UQAM-2023-2026/SYNAPSE/scripts/Python/DT/NSGA-II/data/BottomFloor.png

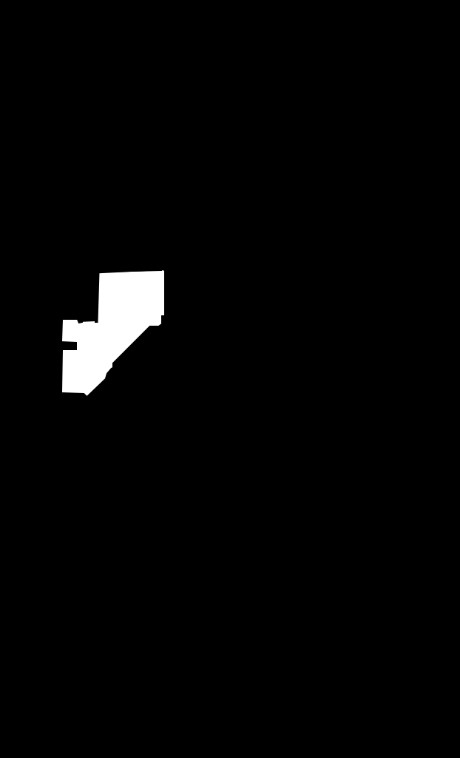
scripts/Python/DT/NSGA-II/data/BottomFloor.png
