UQAM-2023-2026/SYNAPSE/scripts/Python/DT/NSGA-II/data/Full-Plan - SB.png

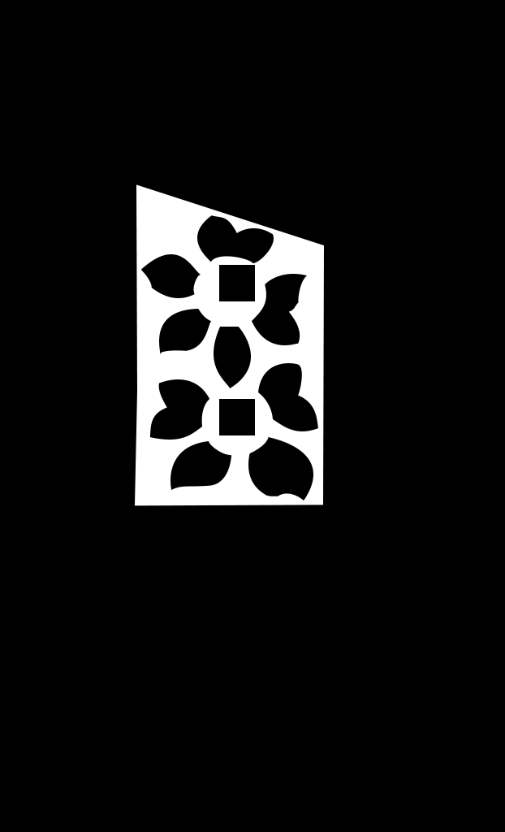
scripts/Python/DT/NSGA-II/data/Full-Plan - SB.png
