UQAM-2023-2026/SYNAPSE/scripts/Python/DT/NSGA-II/data/placeable.png

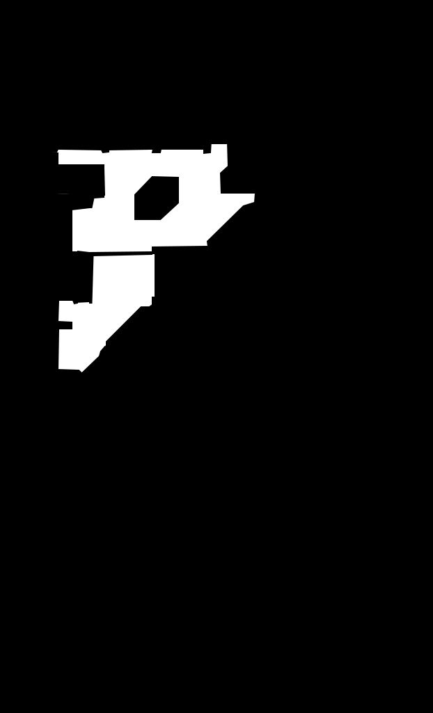
scripts/Python/DT/NSGA-II/data/placeable.png
