UQAM-2023-2026/SYNAPSE/assets/3dmodel/noeud/ESPCASE/espcase4.3mf

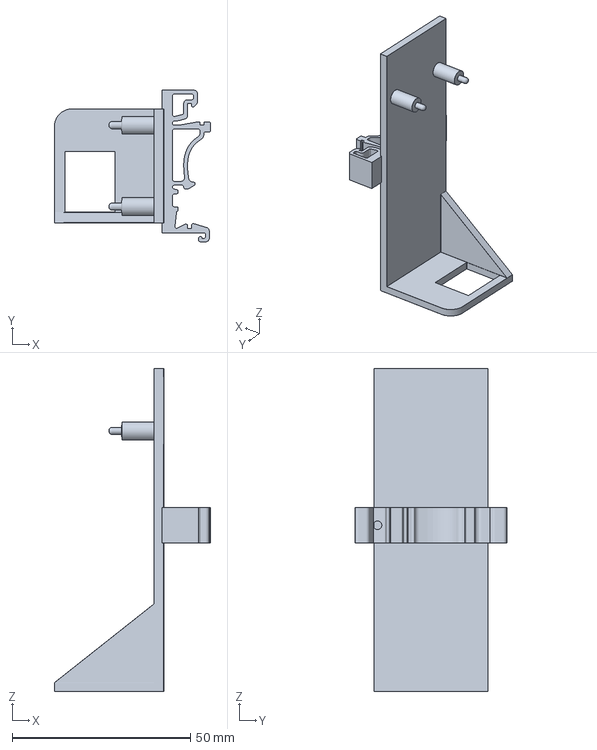
[picture p21: CAD file, 2026-01-28]
assets/3dmodel/noeud/ESPCASE/espcase4.3mf
43.9 x 42.6 x 90.7 mm
