UQAM-2023-2026/SYNAPSE/assets/3dmodel/Rhizome/v2/Middle_V2.stl

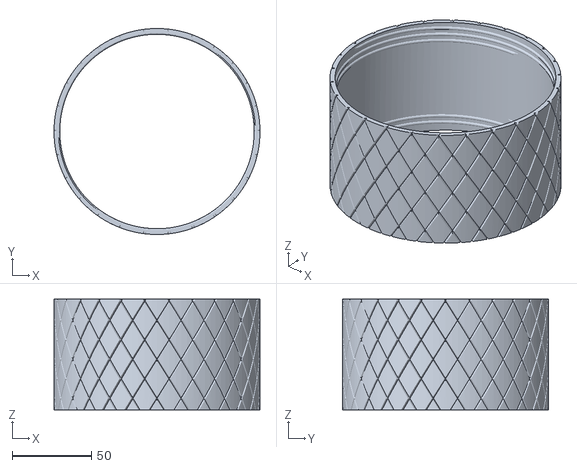
[picture p22: CAD file, 2025-12-05]
assets/3dmodel/Rhizome/v2/Middle_V2.stl
130.0 x 130.0 x 70.0
