UQAM-2023-2026/SYNAPSE/assets/3dmodel/noeud/ESPCASE/espbonsens.stl

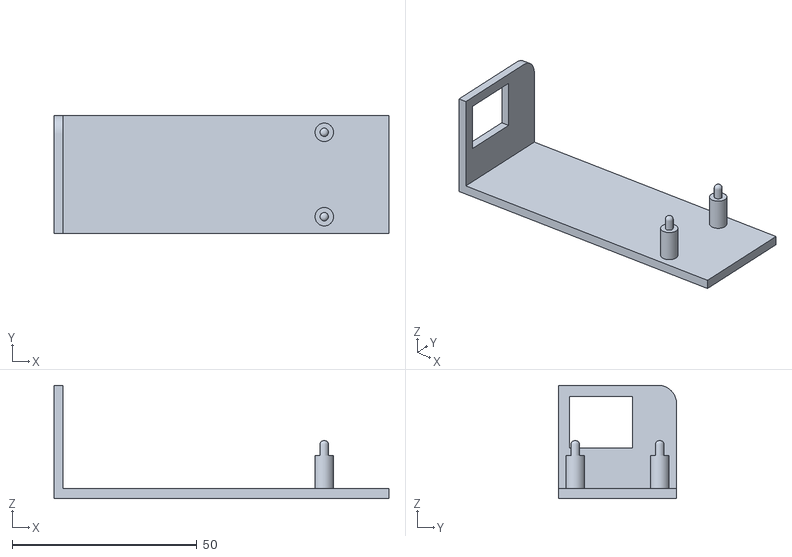
[picture p23: CAD file, 2026-01-22]
assets/3dmodel/noeud/ESPCASE/espbonsens.stl
90.7 x 32.0 x 30.7
