UQAM-2023-2026/SYNAPSE/assets/3dmodel/noeud/ESPCASE/espcase2.stl

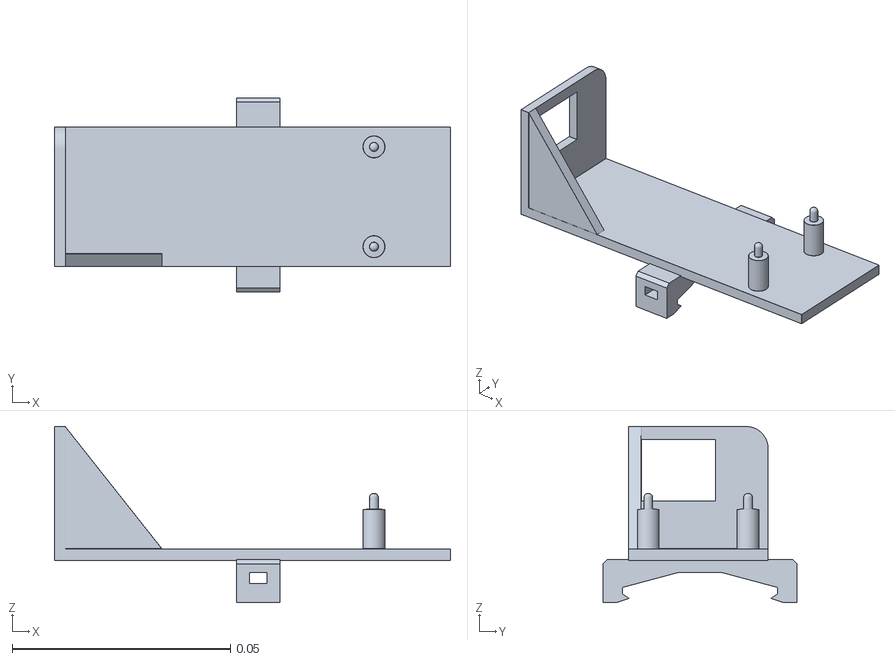
[picture p24: CAD file, 2026-01-22]
assets/3dmodel/noeud/ESPCASE/espcase2.stl
0.0907 x 0.0445 x 0.0404
