UQAM-2023-2026/SYNAPSE/assets/3dmodel/noeud/ESPCASE/espcase1.stl

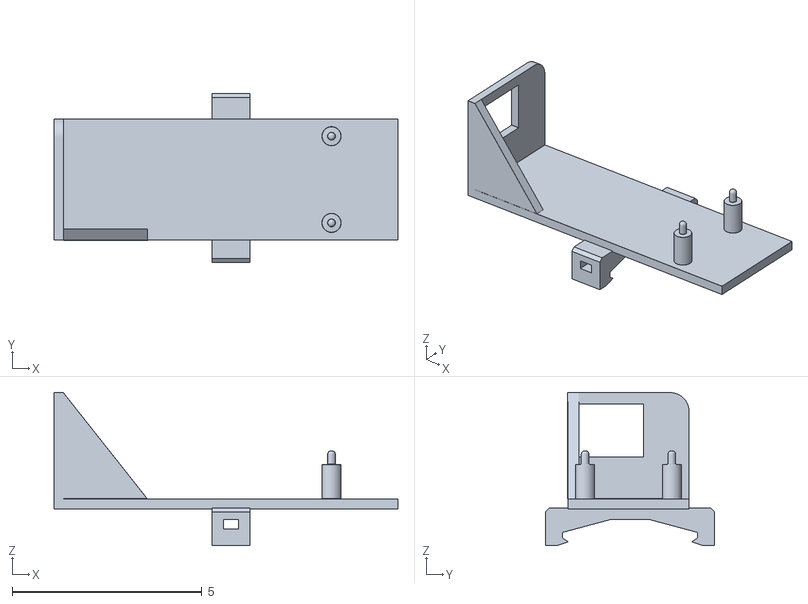
[picture p25: CAD file, 2026-01-22]
assets/3dmodel/noeud/ESPCASE/espcase1.stl
9.07 x 4.45 x 4.04
