UQAM-2023-2026/SYNAPSE/src/Arduino/Scenographie/version precedente/debugbouton/debugbouton.ino

const int buttonPin = 9;  // the number of the pushbutton pin

// variables will change:
int buttonState = 0;  // variable for reading the pushbutton status

void setup() {

  Serial.begin(9600); // Pour le débogage sur l'écran PC
  // initialize the pushbutton pin as an input:
  pinMode(buttonPin, INPUT);
}

void loop() {
  // read the state of the pushbutton value:
  buttonState = digitalRead(buttonPin);

  // check if the pushbutton is pressed. If it is, the buttonState is HIGH:
  if (buttonState == HIGH) {
    // turn LED on:
    Serial.println("high");
  } else {
    // turn LED off:
    Serial.println("low");
  }
}
