UQAM-2023-2026/SYNAPSE/src/Arduino/Noeud/CodeNoeudV5-rhiz/src/main.cpp

/*
 * Simulateur de Nœud - Pour tester la communication Rhizome/Nœud
 * 
 * Connecter un Teensy avec ce code via Serial2 au right d'un rhizome
 * Le nœud répondra automatiquement aux messages /discover
 */

#include <Arduino.h>
#include <MicroOscSlip.h>

#define SERIAL_BAUD 9600
#define NODE_DRAIN_RATE 5.0f  // Énergie/seconde à drainer

MicroOscSlip<32> oscNode(&Serial2);

void setup() {
  Serial.begin(115200);
  Serial2.begin(SERIAL_BAUD);
  
  Serial.println("=== NODE SIMULATOR STARTED ===");
  Serial.print("Drain rate: ");
  Serial.println(NODE_DRAIN_RATE);
  Serial.println("Waiting for rhizomes...");
}

void handleNodeMessage(MicroOscMessage &msg) {
  if (msg.checkOscAddress("/discover")) {
    int origin = msg.nextAsInt();
    int count = msg.nextAsInt();
    
    Serial.println("---");
    Serial.print("[RECV] /discover from rhizome ");
    Serial.print(origin);
    Serial.print(" (chain of ");
    Serial.print(count);
    Serial.println(" rhizomes)");
    
    // Respond with /node message
    // The rhizome chain will handle routing the drain to the last rhizome
    delay(50); // Small delay to ensure message is processed
    oscNode.sendMessage("/node", "f", NODE_DRAIN_RATE);
    
    Serial.print("[SEND] /node drainRate=");
    Serial.println(NODE_DRAIN_RATE);
    Serial.println("  → Chain updated, last rhizome will drain");
    Serial.println("---");
    
  } else if (msg.checkOscAddress("/energy")) {
    int rhizomeId = msg.nextAsInt();
    float energy = msg.nextAsFloat();
    
    Serial.print("[ENERGY] Rhizome ");
    Serial.print(rhizomeId);
    Serial.print(" reporting energy: ");
    Serial.println(energy);
    
    if (energy <= 5) {
      Serial.println("  ⚠️  WARNING: Rhizome nearly depleted!");
    }
  }
}

void loop() {
  // Listen for messages from rhizomes
  oscNode.onOscMessageReceived(handleNodeMessage);
  
  delay(10);
}
